cherry-takuan/nlp/nlp-16a/Hardware/Y_BUS_Ctrl/基板プレビュー.pdf

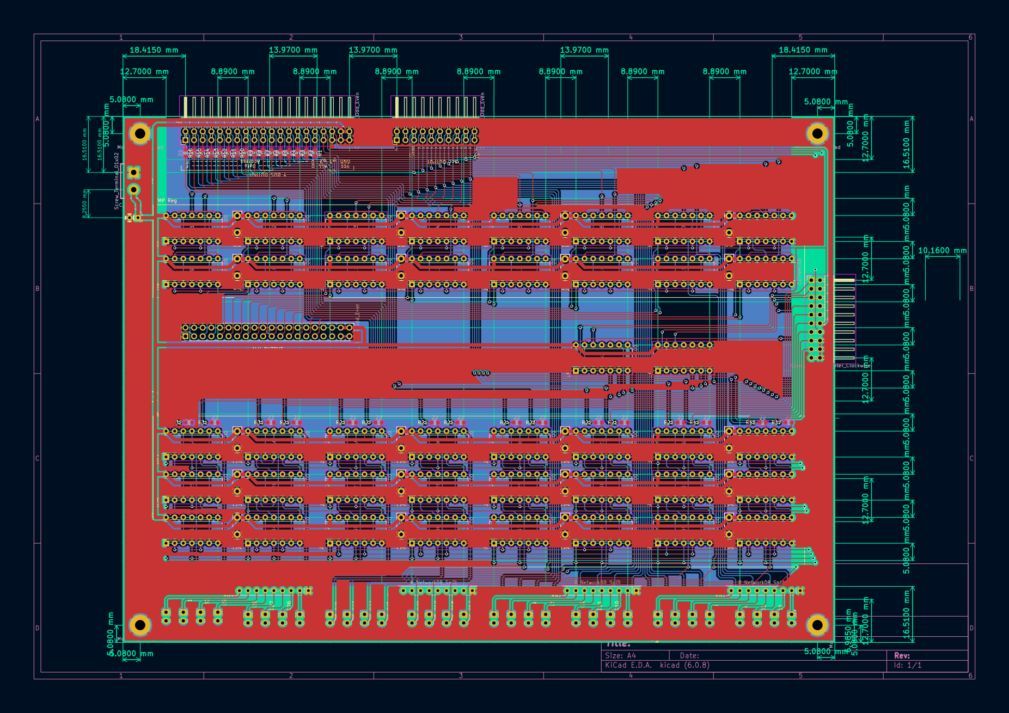
[picture p171: page 1]
