cherry-takuan/nlp/nlp-16a/Hardware/alu_c/基板プレビュー.pdf

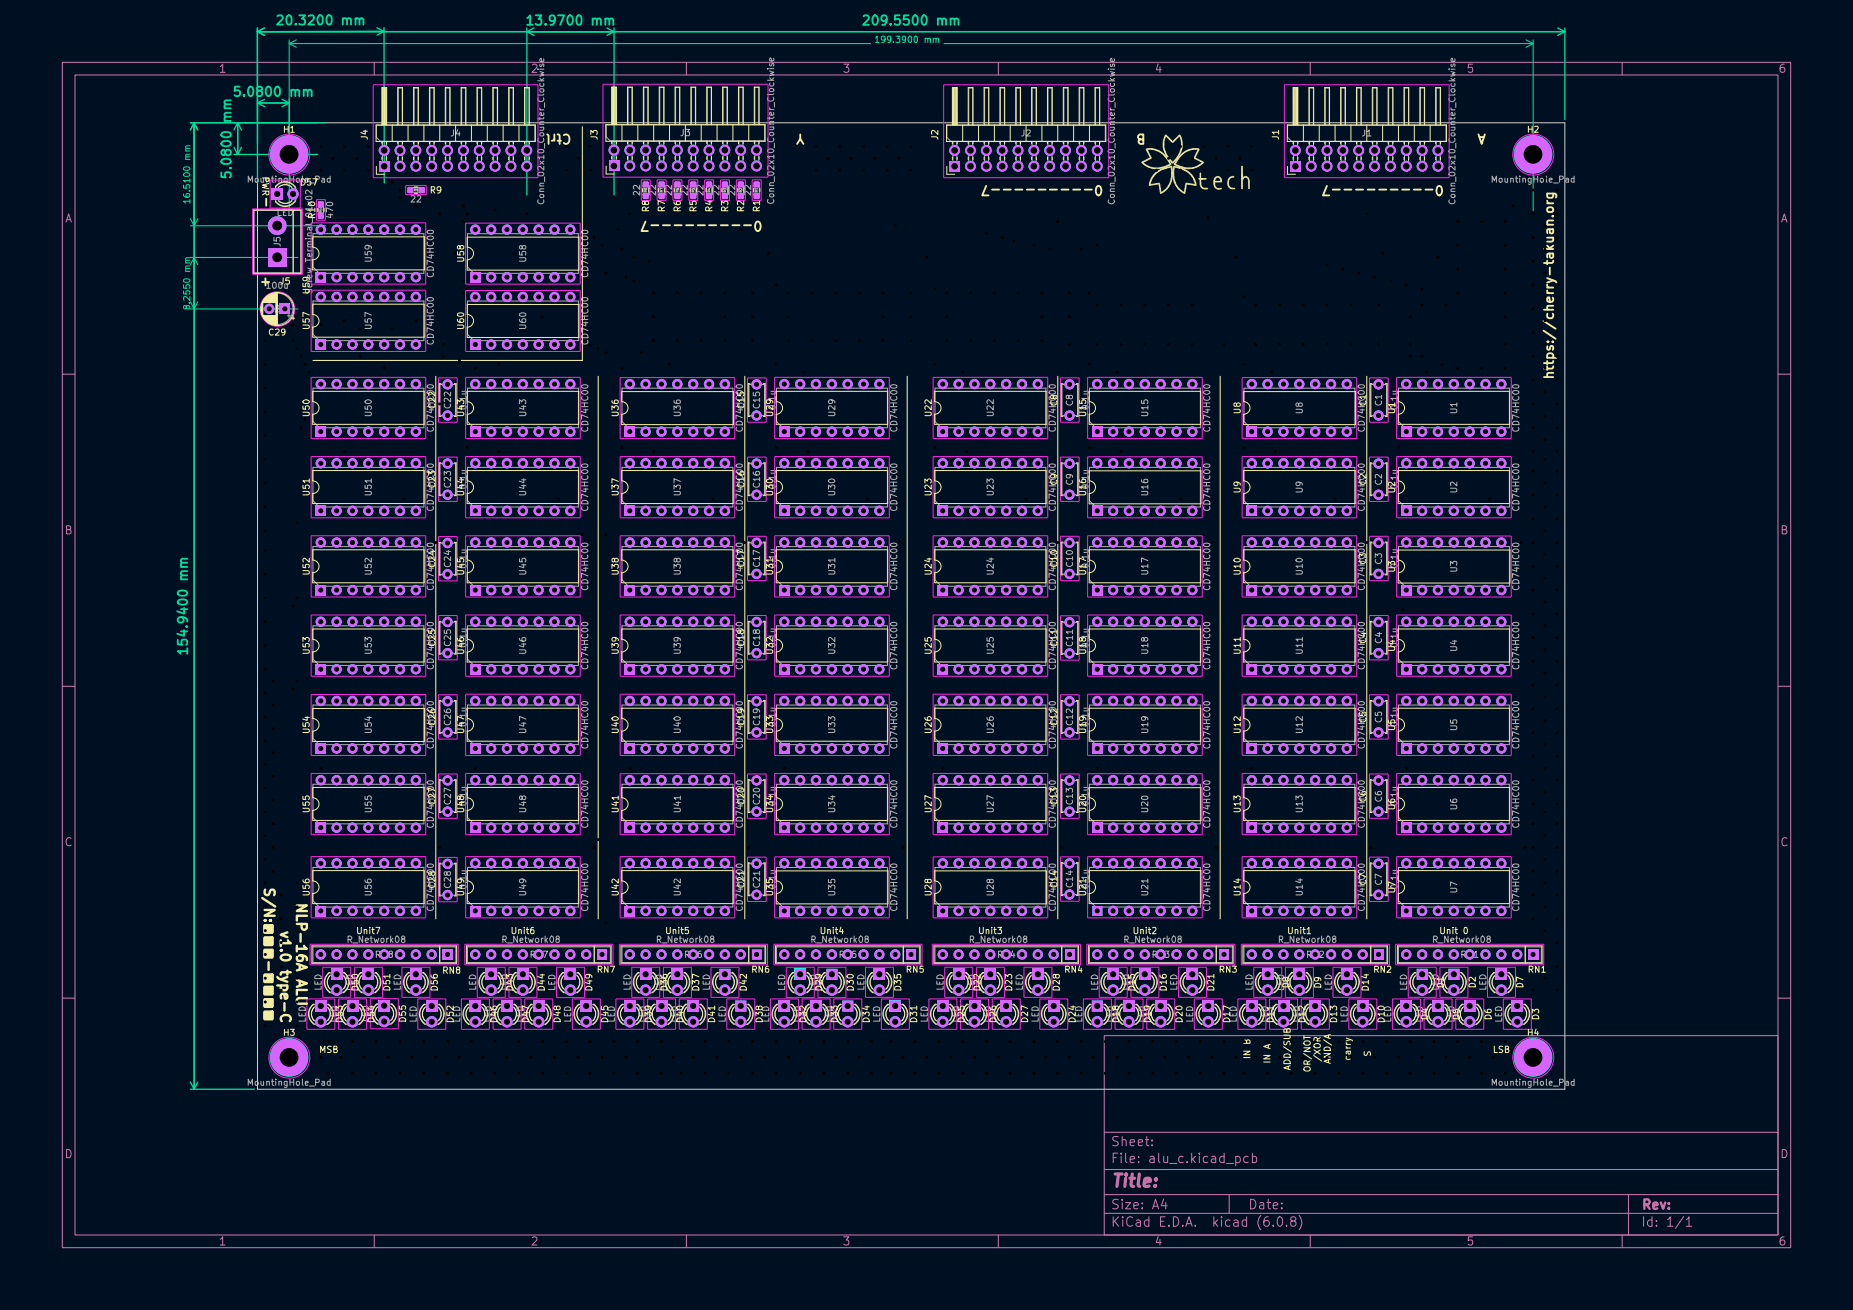
[picture p172: page 1]
