cherry-takuan/nlp/nlp-16a/Hardware/alu_ctrl/基板プレビュー.pdf

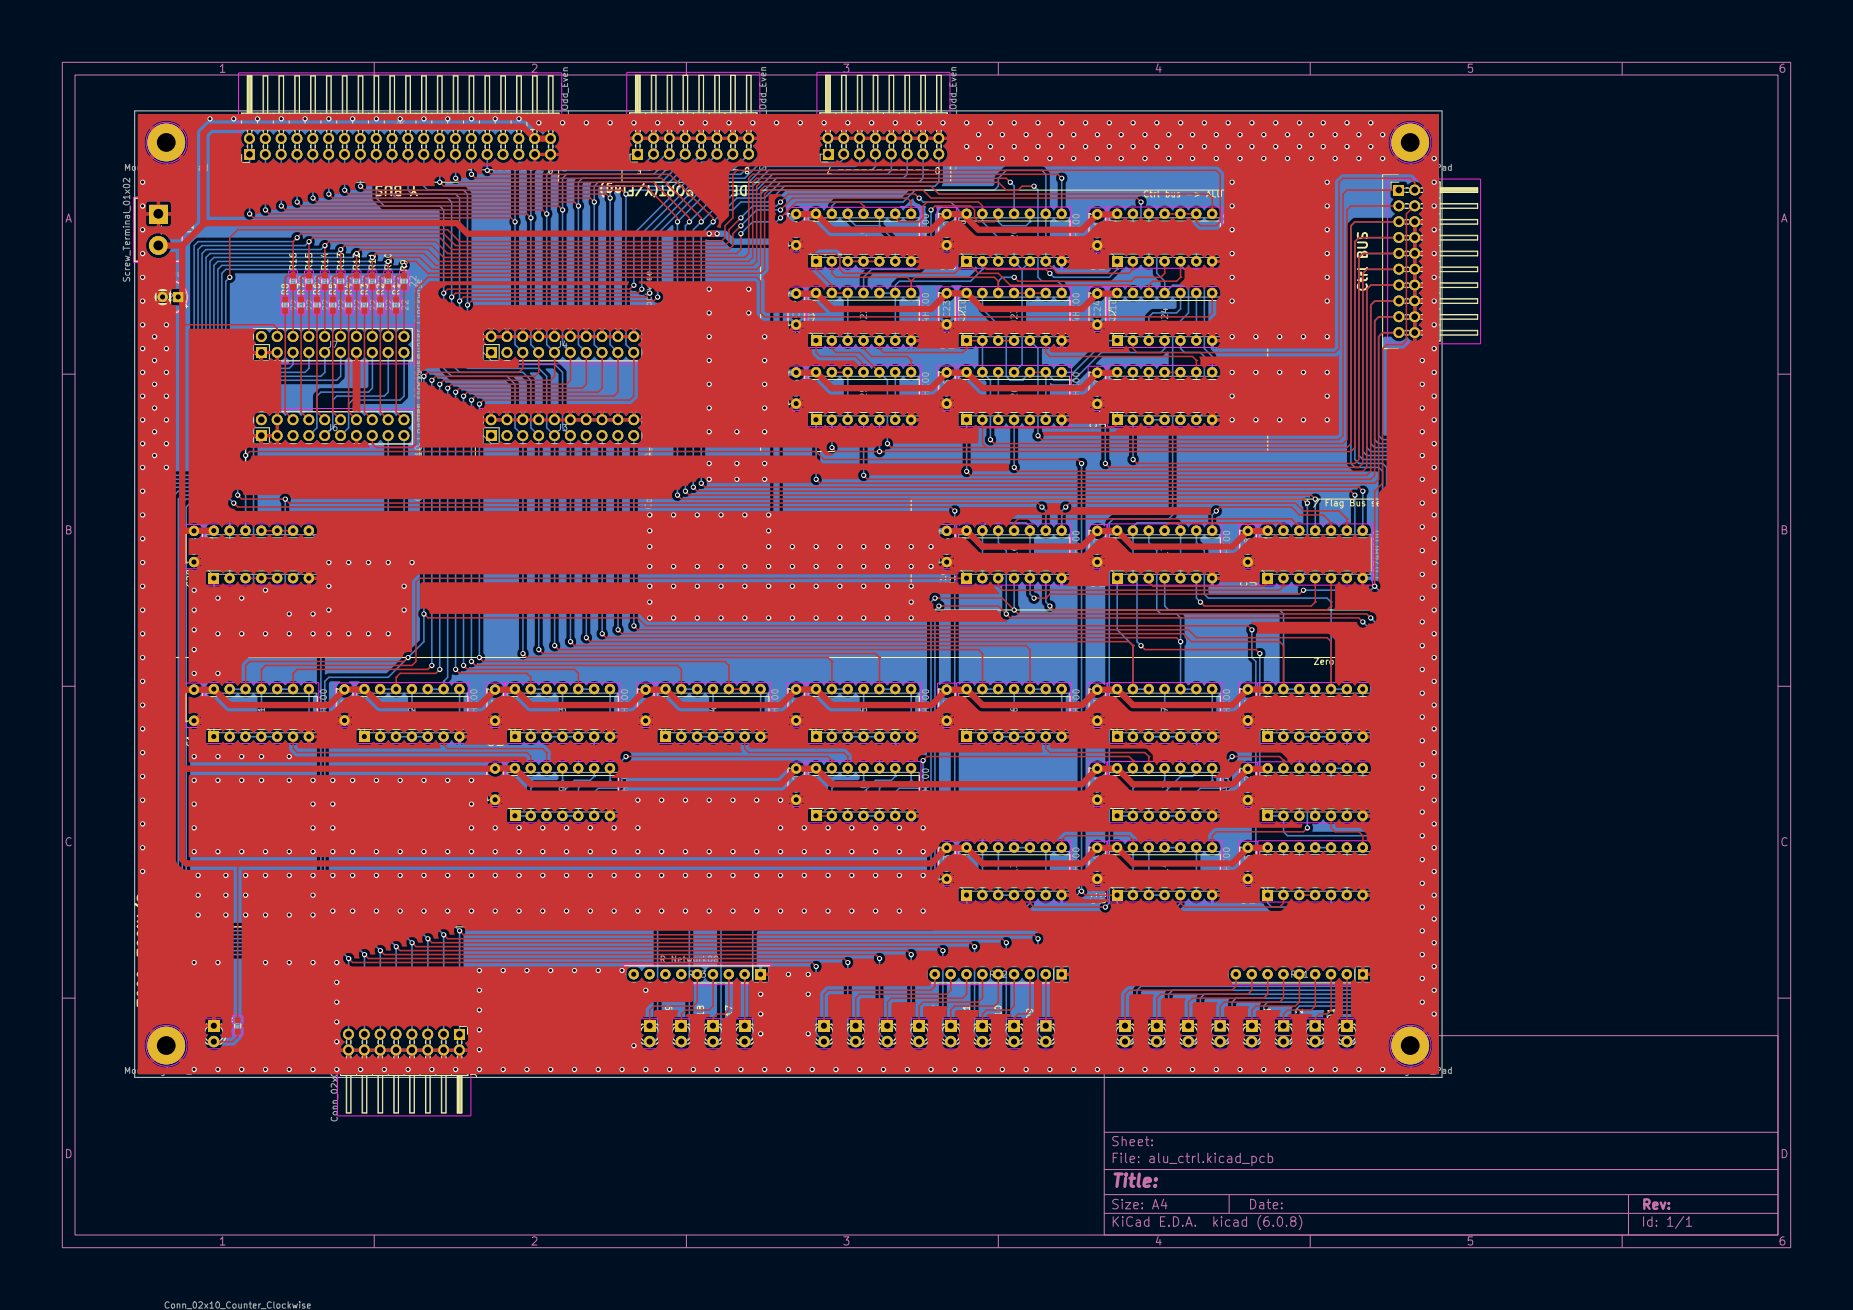
[picture p173: page 1]
