cherry-takuan/nlp/nlp-16a/Hardware/SW_Board/SW_Board.kicad_pcb

## KiCad design nlp-16a/Hardware/SW_Board/SW_Board.kicad_pcb (2023-10-30)

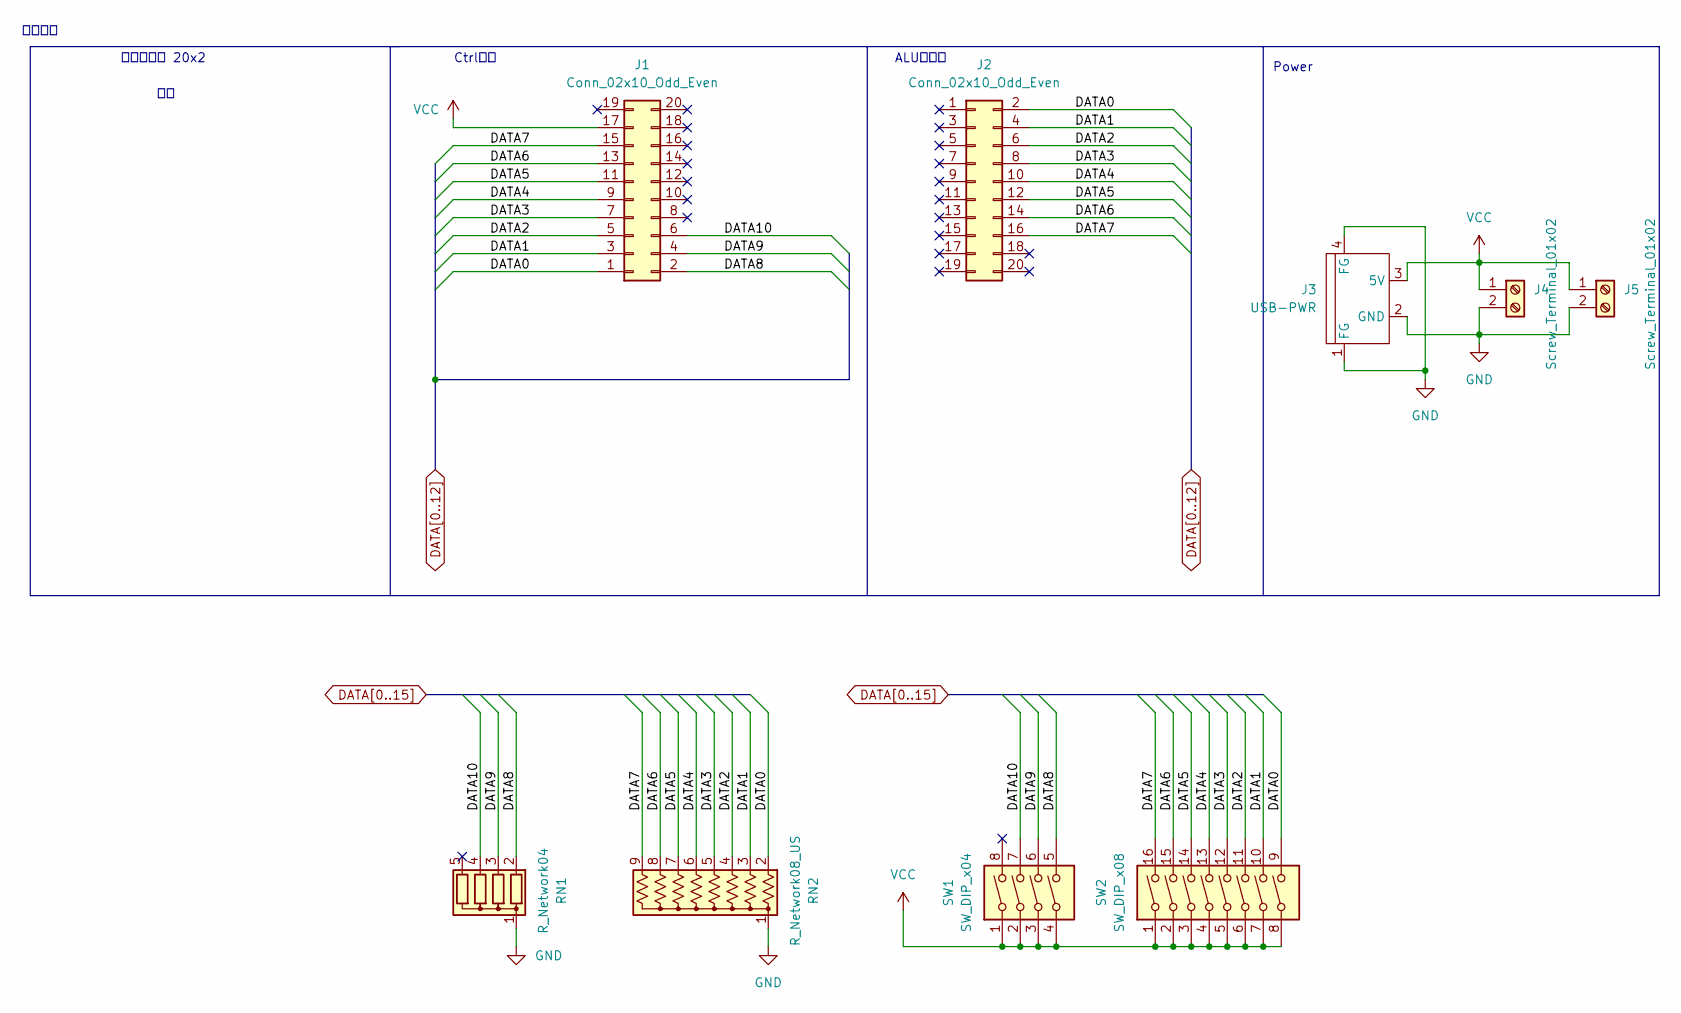
[picture p218: schematic SW_Board.kicad_sch]

Parts:
J1, J2: Conn_02x10_Odd_Even; PinHeader_2x10_P2.54mm_Vertical
J3: USB-PWR
J4, J5: Screw_Terminal_01x02; TerminalBlock_bornier-2_P5.08mm
RN1: R_Network04; R_Array_SIP5
RN2: R_Network08_US; R_Array_SIP9
SW1: SW_DIP_x04; SW_DIP_SPSTx04_Slide_6.7x11.72mm_W7.62mm_P2.54mm_LowProfile
SW2: SW_DIP_x08; SW_DIP_SPSTx08_Slide_6.7x21.88mm_W7.62mm_P2.54mm_LowProfile

Connections:
DATA0: J1.1, J2.2, RN2.2 (R1), SW2.9
DATA1: J1.3, J2.4, RN2.3 (R2), SW2.10
DATA2: J1.5, J2.6, RN2.4 (R3), SW2.11
DATA3: J1.7, J2.8, RN2.5 (R4), SW2.12
DATA4: J1.9, J2.10, RN2.6 (R5), SW2.13
DATA5: J1.11, J2.12, RN2.7 (R6), SW2.14
DATA6: J1.13, J2.14, RN2.8 (R7), SW2.15
DATA7: J1.15, J2.16, RN2.9 (R8), SW2.16
DATA8: J1.2, RN1.2 (R1), SW1.5
DATA9: J1.4, RN1.3 (R2), SW1.6
DATA10: J1.6, RN1.4 (R3), SW1.7
GND: J3.1 (FG), J3.2 (GND), J3.4 (FG), J4.2, J5.2, RN1.1 (common), RN2.1 (common)
VCC: J1.17, J3.3 (5V), J4.1, J5.1, SW1.1, SW1.2, SW1.3, SW1.4, SW2.1, SW2.2, SW2.3, SW2.4, SW2.5, SW2.6, SW2.7, SW2.8

Notes on the sheet:
接続関係
Ctrlバス
汎用データ 20x2
Power
ALUデータ

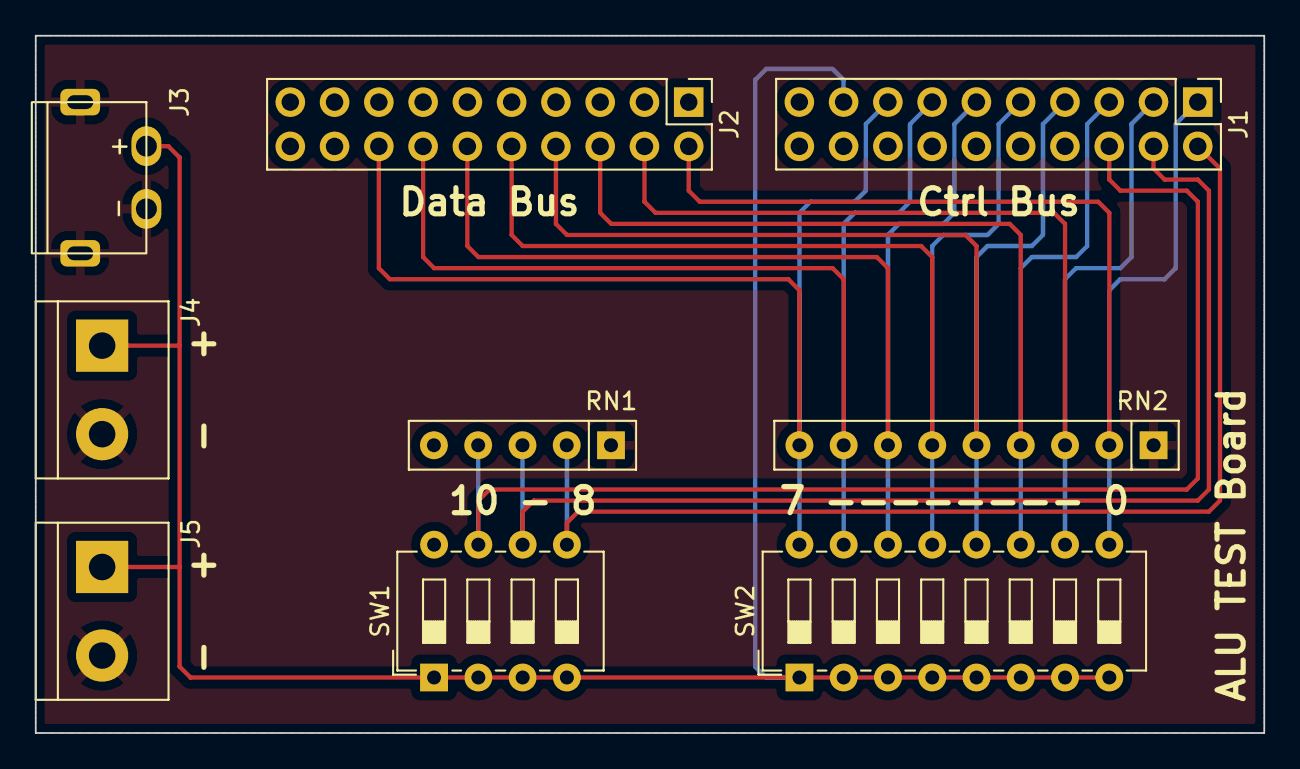
[picture p219: board SW_Board.kicad_pcb from above]

Board: 2 copper layers, 70.5 x 40.0 mm, 9 parts (0 on the bottom side), 13 nets.
