cherry-takuan/nlp/nlp-16a/Software/debugger/Reg/main.py

import nlp_debug
from time import sleep

A_PATTERN = [
        0x0000,
        0x1234,
        0x5555,
        0xAAAA,
        0xFFFF,
    ]
def clk(id,address):
    phi1 = 1
    phi2 = 0
    debug.output(id,(address<<10) | 0b1111111111 | phi1<<15 | phi2<<14)
    phi1 = 0
    phi2 = 0
    debug.output(id,(address<<10) | 0b1111111111 | phi1<<15 | phi2<<14)
    phi1 = 0
    phi2 = 1
    debug.output(id,(address<<10) | 0b1111111111 | phi1<<15 | phi2<<14)
    phi1 = 0
    phi2 = 0
    debug.output(id,(address<<10) | 0b1111111111 | phi1<<15 | phi2<<14)
    return

if __name__ == '__main__':
    debug = nlp_debug.debugger()

    debug.reset()
    id = debug.scan_devides()
    if id != 4:
        del debug
        exit()
    
    A_BUS_CTRL = 0x00
    Y_BUS_CTRL = 0x01
    ALU_CTRL = 0x02
    IO_BUS = 0x03

    debug.dir_set(A_BUS_CTRL,0xFFFF)
    debug.dir_set(Y_BUS_CTRL,0xFFFF)
    debug.dir_set(ALU_CTRL,0x0FFF)
    debug.dir_set(IO_BUS,0x0000)
    debug.execute(IO_BUS,"REVERSE_MODE",0x0001)

    IO_ADDRESS = 11
    phi1 = 0
    phi2 = 0
    debug.output(Y_BUS_CTRL,(0x0F<<10) | 0b1111111111 | phi1<<15 | phi2<<14)    #出力先を適当に設定
    debug.dir_set(IO_BUS,0x0000)
    debug.output(A_BUS_CTRL,(0x0F<<10) | 0b1111111111)                    #入力をIOに設定
    debug.output(ALU_CTRL,0b011101001001)#ALU転送命令
    for A in range(0x10):
        clk(Y_BUS_CTRL,A)
    del debug
