cherry-takuan/nlp/nlp-16a/Hardware/alu_ctrl/decoder/Ctrl-ALU_decode/decoder_ALU2.v

module decode_ALU2(Ctrl0,Ctrl1,Ctrl2,Ctrl3,Ctrl4,Ctrl5,c_flag,ALU2_out);
    input Ctrl0,Ctrl1,Ctrl2,Ctrl3,Ctrl4,Ctrl5,c_flag;
    output ALU2_out;
    wire tmp1,tmp2;
    NAND NAND1(~Ctrl0,~Ctrl1,tmp1);
    NAND NAND2(tmp1,tmp1,tmp2);
    NAND NAND3(tmp2,~Ctrl2,ALU2_out);
endmodule
